worshix/pin-hole-detector/media/captures/2026/05/30/esp32cam_20260530_201952_285666.jpg

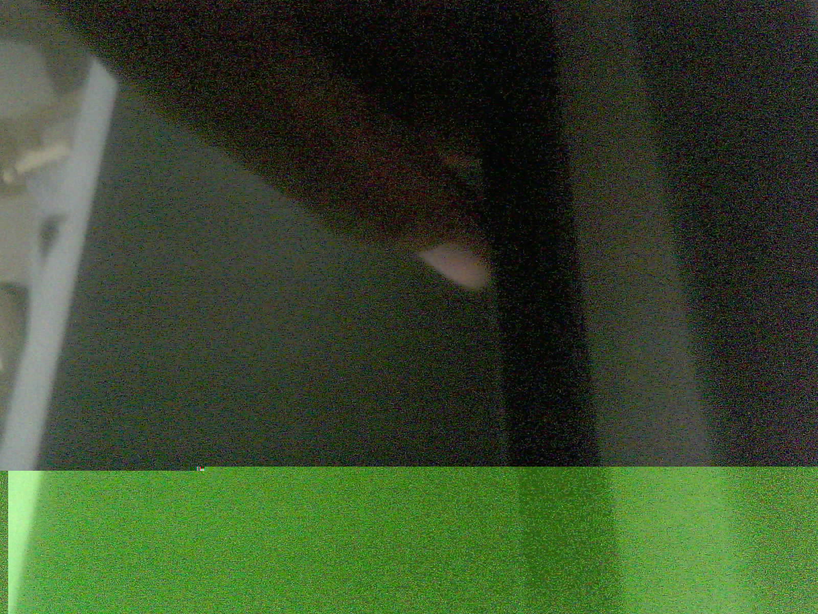
media/captures/2026/05/30/esp32cam_20260530_201952_285666.jpg
