worshix/pin-hole-detector/media/captures/2026/05/30/esp32cam_20260530_202204_994718.jpg

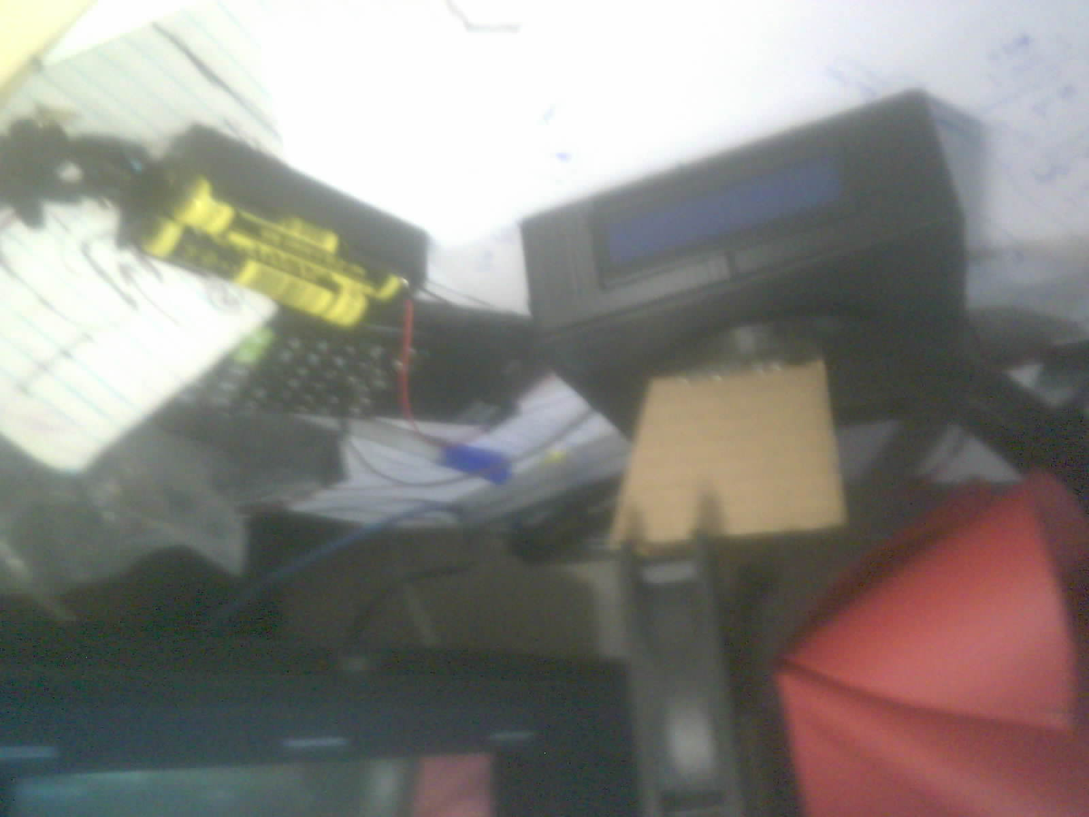
media/captures/2026/05/30/esp32cam_20260530_202204_994718.jpg
